smierx/FHBSHK/ImageProcessing/configs/1606282529/0.tif

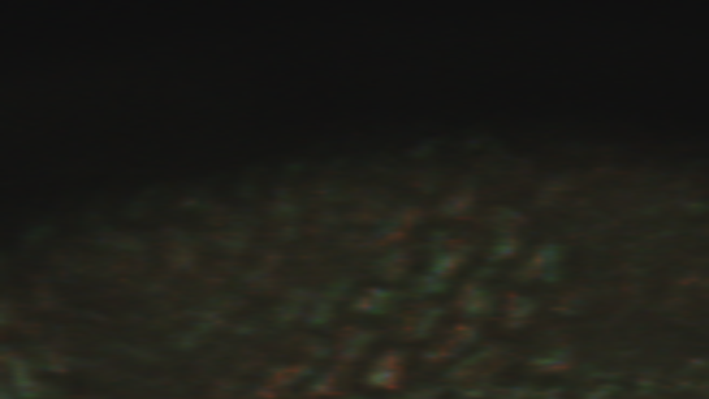
ImageProcessing/configs/1606282529/0.tif
