smierx/FHBSHK/ImageProcessing/configs/1606282529/1.tif

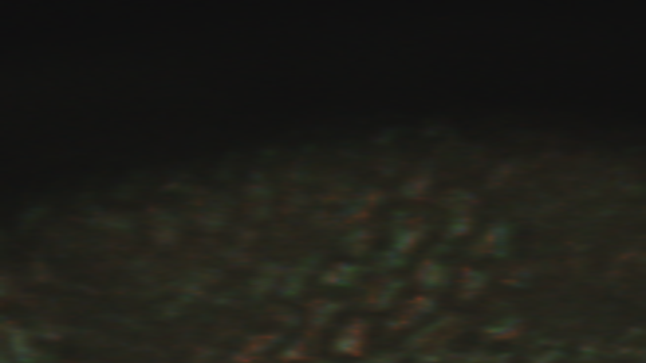
ImageProcessing/configs/1606282529/1.tif
