smierx/FHBSHK/ImageProcessing/configs/1606282529/2.tif

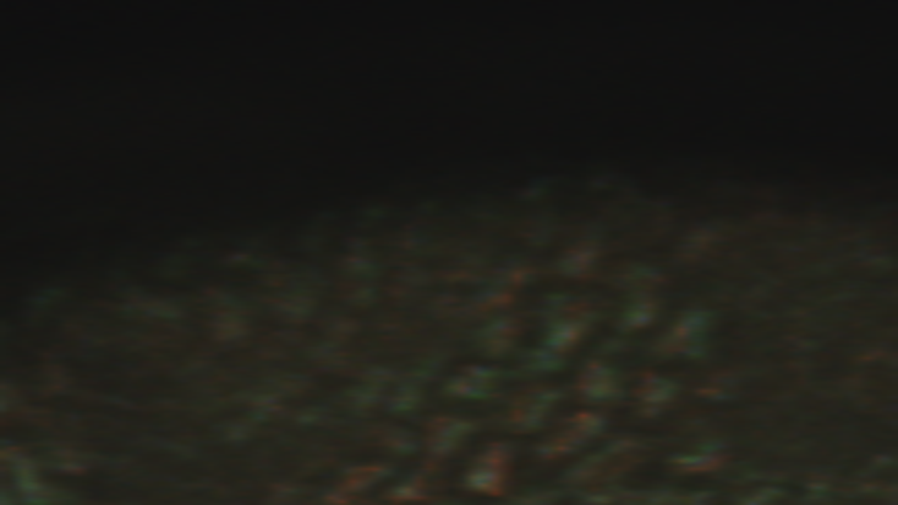
ImageProcessing/configs/1606282529/2.tif
