smierx/FHBSHK/ImageProcessing/configs/1606282529/7.tif

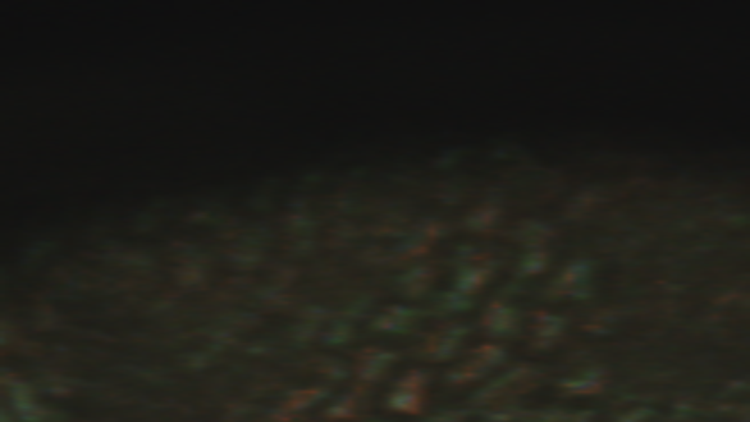
ImageProcessing/configs/1606282529/7.tif
